trisp3ar/BNV-BatteryPack/Documentation/Models and Simulations/over-discharge_protection_2S2P.asc

Bat1: voltage; 8
Bat2: voltage; 8
C1: cap; 100n
C2: cap; 1n
C3: cap; 1n
D1: zener; BZX84B6V2L
D2: zener; BZX84B6V2L
M1: pmos; RSL020P03
M2: pmos; RSL020P03
NODs: res; 12
R1: res; 0.1Meg
R2: res; 1.3Meg
R3: res; 0.6Meg
R4: res; 0.402k
R5: res; 5Meg
R6: res; 1Meg
R7: res; 0.1Meg
R8: res; 0.6Meg
R9: res; 1Meg
R10: res; 1.3Meg
R11: res; 0.402k
R12: res; 5Meg
U3: MAX9944
Named nets: 0, Vcc, V_out
.dc Bat1 8.4 4 0.1 Bat2 8.4 4 0.1
BNV-Battery Pack undervoltage protection
 
Explanation:
The circuit checks for voltage of 2S2P
Two circuits for 4 cells total
When the voltage of one cell stack drops below 5.7 V,
the P-Ch MOSFET will block.
 
The Output of the circuit can later be regulated.
include MAX9944.cir
